drewsum/Nixie_Clock/rev_a/Nixie Clock/Nixie Clock Poster/RefDes.pdf

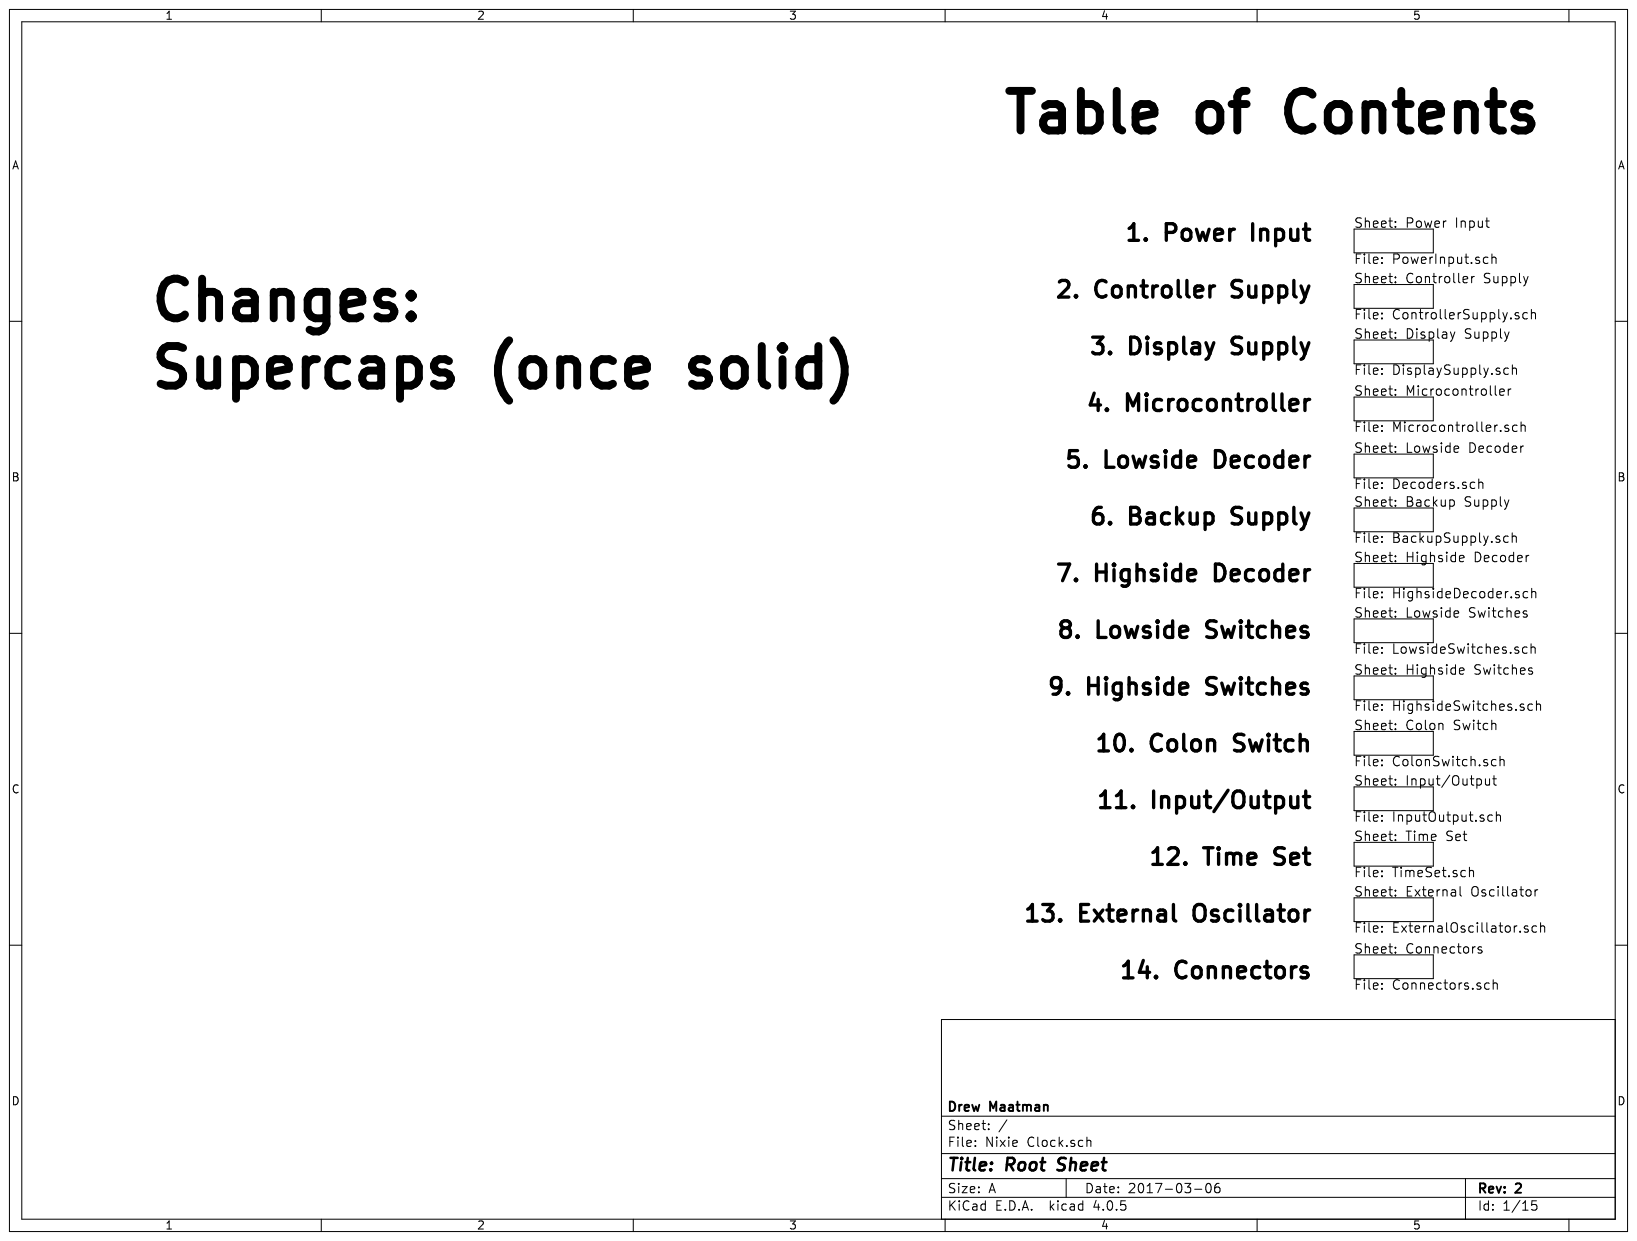
[picture p72: page 1]






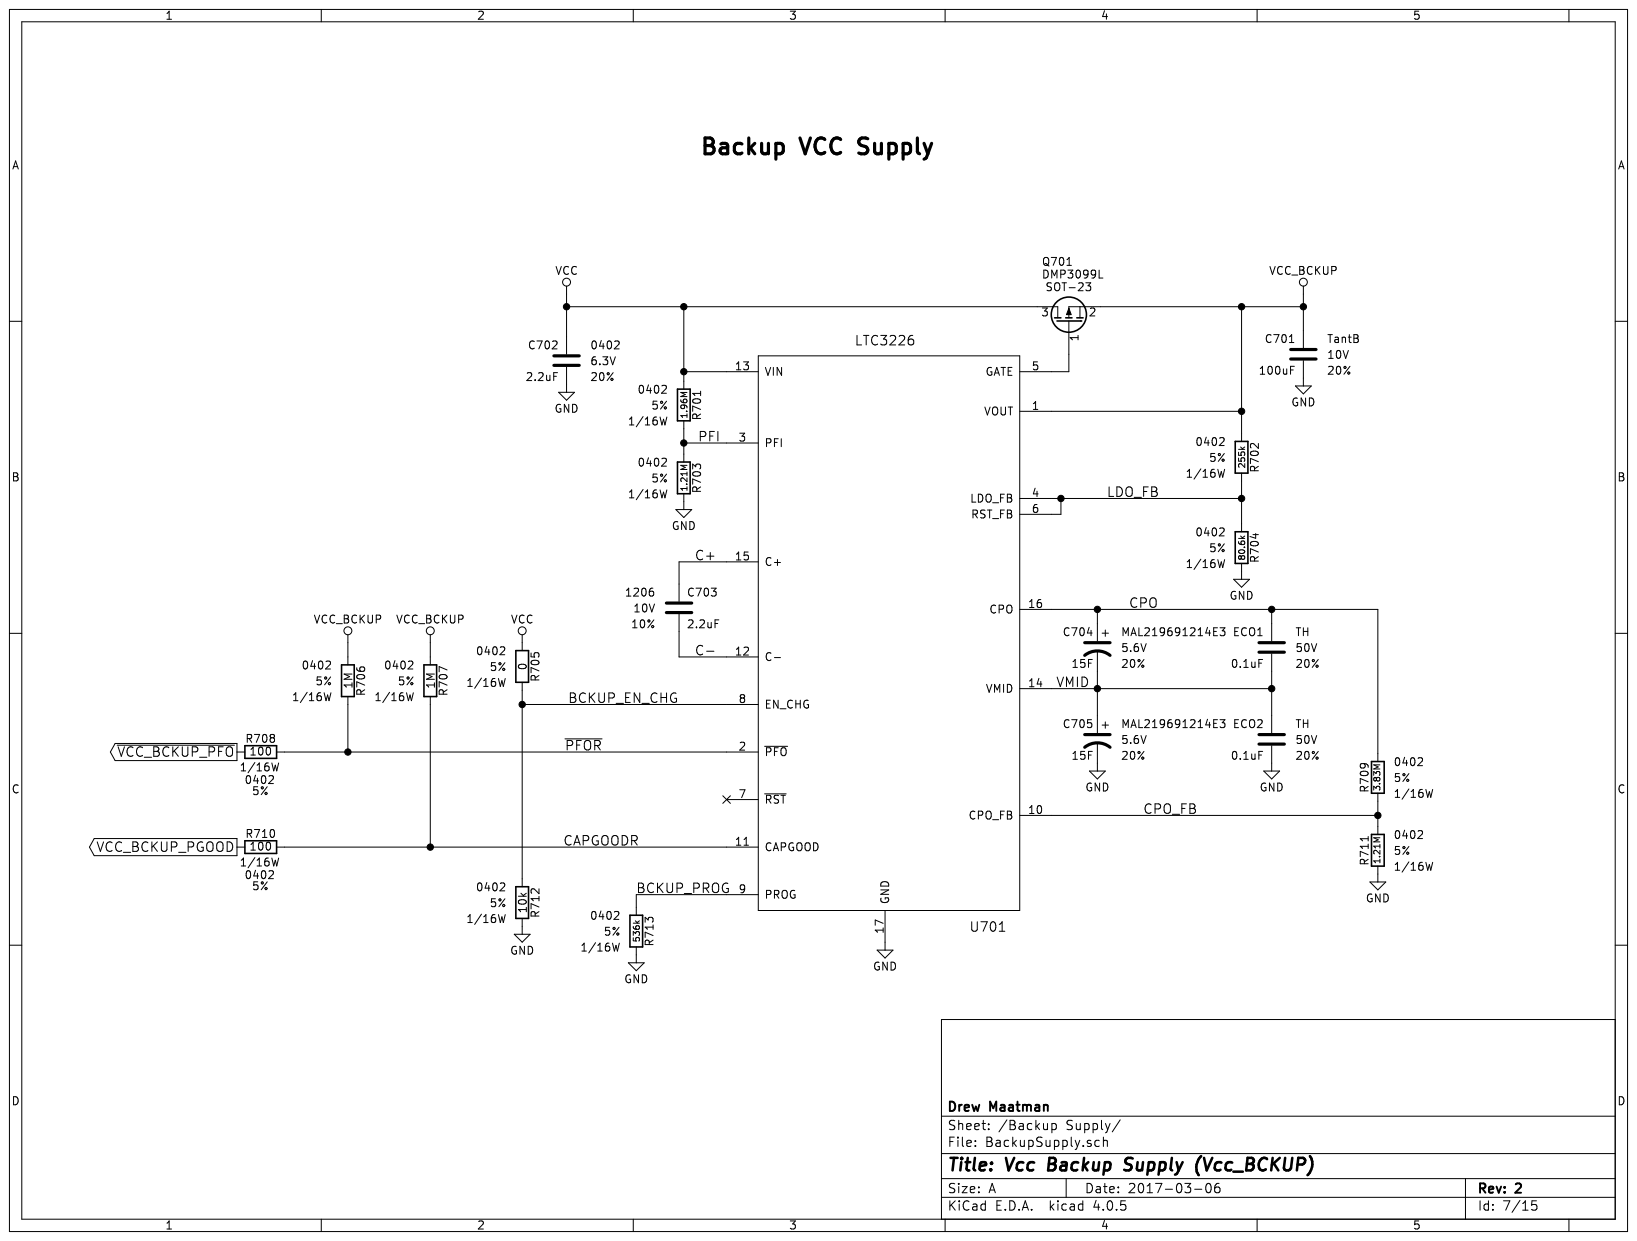
[picture p73: page 7]
