drewsum/Nixie_Clock/rev_b/hdw/Nixie_Clock_Core/design_files/POS180_boost.asc

C1: cap; 0.1µ
C2: cap; .01µ
C3: polcap; 4.7µ
C4: cap; 0.01µ
C5: cap; 0.1µ
C6: cap; 0.1µ
C7: cap; 1.5µ
D1: diode; RRU1LAM4S
D2: diode; RRU1LAM4S
D3: diode; RRU1LAM4S
I1: current; PULSE(0 5m 20m 0.1u 0.1u 0.5m 1m)
L1: ind; 680µ
Q1: NMOS; IRFP240
R1: RES; 14k
R2: res; 28.7k
R3: res; 1.6Meg
R4: res; 100k
R5: res; 330
R6: res; 200K
R7: res; 0.36
R8: res; 3.4k
R9: res; 1.6Meg
R10: res; 10k
R11: res; 1.33k
R12: res; 6.49k
R13: res; 1.6Meg
R14: res; 10k
U1: LT3757A
U2: LT6700-1
U3: LT6700-1
V1: VOLTAGE; 24
V2: voltage; 3.3
Named nets: 0, IN, POS180, POS90, pos3p3, pos180_pgood, pos90_pgood
.tran 100m startup
