drewsum/Nixie_Clock/rev_b/sfw/U1001_Firmware/Nixie_Clock.X/temperature_sensors.h

/* ************************************************************************** */
/** Descriptive File Name

  @Company
    Company Name

  @File Name
    filename.h

  @Summary
    Brief description of the file.

  @Description
    Describe the purpose of this file.
 */
/* ************************************************************************** */

#ifndef _TEMPERATURE_SENSORS_H    /* Guard against multiple inclusion */
#define _TEMPERATURE_SENSORS_H

#include "mcp9804_temp_sensor.h"

#include "error_handler.h"

// These are all the I2C 7 bit addresses of temperature sensors in this project
#define POS24_TEMP_SNS_ADDR         0x18
#define POS3P3_TEMP_SNS_ADDR        0x19
#define POS180_TEMP_SNS_ADDR        0x1A
#define AMB_TEMP_SNS_ADDR           0x1C

volatile __attribute__((coherent)) uint8_t temp_sense_data_request = 0;

// This function initializes all temperature sensors in the project, if available
void tempSensorsInitialize(void);

// this function gets temperature data for all temperature sensors
void tempSensorsRetrieveData(void);

// this function prints out the status for all temperature sensors
void printTemperatureSensorStatus(void);

#endif /* _TEMPERATURE_SENSORS_H */

/* *****************************************************************************
 End of File
 */
