drewsum/Nixie_Clock/rev_b/sfw/U1001_Firmware/Nixie_Clock.X/adc_channels.c

#include "adc_channels.h"

#include <stdio.h>

#include "32mz_interrupt_control.h"
#include "telemetry.h"
#include "terminal_control.h"
#include "pin_macros.h"

/*
 * 
 * Used ADC channels: 
 * 
 * AN19 - POS90_ADC
 * AN20 - POS180_ADC
 * AN21 - VBAT ADC
 * AN43 - Internal VREF
 * AN44 - Die Temp
 * 
 * */

// this function sets up ADC channels
void adcChannelsInitialize(void) {
 
    /* Select ADC input mode for each channel*/
    ADCIMCON2bits.DIFF19 = 0; // Single ended mode
    ADCIMCON2bits.SIGN19 = 0; // unsigned data format
    ADCIMCON2bits.DIFF20 = 0; // Single ended mode
    ADCIMCON2bits.SIGN20 = 0; // unsigned data format
    if (RTC_HARDSTRAP_PIN == 0) {
        ADCIMCON2bits.DIFF21 = 0; // Single ended mode
        ADCIMCON2bits.SIGN21 = 0; // unsigned data format
    }
    ADCIMCON3bits.DIFF43 = 0; // Single ended mode
    ADCIMCON3bits.SIGN43 = 0; // unsigned data format
    ADCIMCON3bits.DIFF44 = 0; // Single ended mode
    ADCIMCON3bits.SIGN44 = 0; // unsigned data format
    
    /* Configure interrupt enables */
    ADCGIRQEN1bits.AGIEN19 = 1;     // enable data ready 19 IRQ
    ADCGIRQEN1bits.AGIEN20 = 1;     // enable data ready 20 IRQ
    if (RTC_HARDSTRAP_PIN == 0) ADCGIRQEN1bits.AGIEN21 = 1;     // enable data ready 21 IRQ
    ADCGIRQEN2bits.AGIEN43 = 1;     // enable data ready 43 IRQ
    ADCGIRQEN2bits.AGIEN44 = 1;     // enable data ready 44 IRQ
    
    // set IRQ priorities
    setInterruptPriority(ADC_Data_19, 1);
    setInterruptPriority(ADC_Data_20, 1);
    if (RTC_HARDSTRAP_PIN == 0) setInterruptPriority(ADC_Data_21, 1);
    setInterruptPriority(ADC_Data_43, 1);
    setInterruptPriority(ADC_Data_44, 1);
    
    // set IRQ subpriorities
    setInterruptSubpriority(ADC_Data_19, 1);
    setInterruptSubpriority(ADC_Data_20, 1);
    if (RTC_HARDSTRAP_PIN == 0) setInterruptSubpriority(ADC_Data_21, 1);
    setInterruptSubpriority(ADC_Data_43, 2);
    setInterruptSubpriority(ADC_Data_44, 3);
    
    /* Configure common scan */
    ADCCSS1bits.CSS19 = 1;          // Enable Channel 19 for common scan
    ADCCSS1bits.CSS20 = 1;          // Enable Channel 20 for common scan
    if (RTC_HARDSTRAP_PIN == 0) ADCCSS1bits.CSS21 = 1;          // Enable Channel 21 for common scan
    ADCCSS2bits.CSS43 = 1;          // Enable Channel 43 for common scan
    ADCCSS2bits.CSS44 = 1;          // Enable Channel 44 for common scan
    
    // clear interrupt flags
    clearInterruptFlag(ADC_Data_19);
    clearInterruptFlag(ADC_Data_20);
    if (RTC_HARDSTRAP_PIN == 0) clearInterruptFlag(ADC_Data_21);
    clearInterruptFlag(ADC_Data_43);
    clearInterruptFlag(ADC_Data_44);
    
    // enable data ready interrupts
    enableInterrupt(ADC_Data_19);
    enableInterrupt(ADC_Data_20);
    if (RTC_HARDSTRAP_PIN == 0) enableInterrupt(ADC_Data_21);
    enableInterrupt(ADC_Data_43);
    enableInterrupt(ADC_Data_44);
    
}

void __ISR(_ADC_DATA19_VECTOR, IPL1SRS) ADCData19ISR(void) {

    // check to see if data is actually ready
    if (ADCDSTAT1bits.ARDY19) {
        // copy ADC conversion result into telemetry
        telemetry.pos90_termination_voltage = ((double) ADCDATA19) * ADC_VOLTS_PER_LSB * adc_cal_gain * POS90_ADC_GAIN;
        
    }
    
    // clear IRQ
    clearInterruptFlag(ADC_Data_19);
    
}

void __ISR(_ADC_DATA20_VECTOR, IPL1SRS) ADCData20ISR(void) {

    // check to see if data is actually ready
    if (ADCDSTAT1bits.ARDY20) {
        // copy ADC conversion result into telemetry
        telemetry.pos180.voltage =((double) ADCDATA20) * ADC_VOLTS_PER_LSB * adc_cal_gain * POS180_ADC_GAIN;
        
    }
    
    // clear IRQ
    clearInterruptFlag(ADC_Data_20);
    
}

void __ISR(_ADC_DATA21_VECTOR, IPL1SRS) ADCData21ISR(void) {

    // check to see if data is actually ready
    if (ADCDSTAT1bits.ARDY21) {
        // copy ADC conversion result into telemetry
        telemetry.backup_battery_voltage = ((double) ADCDATA21) * ADC_VOLTS_PER_LSB * adc_cal_gain * VBAT_ADC_GAIN;
        
    }
    
    // clear IRQ
    clearInterruptFlag(ADC_Data_21);
    
}

void __ISR(_ADC_DATA43_VECTOR, IPL1SRS) ADCData43ISR(void) {

    // check to see if data is actually ready
    if (ADCDSTAT2bits.ARDY43) {
        // copy ADC conversion result into telemetry
        telemetry.adc_vref_voltage = (double) ADCDATA43 * ADC_VOLTS_PER_LSB;
        // compensate for errors in the ADC, we know VREF is supposed to be 1.2V
        adc_cal_gain = (1.2 / telemetry.adc_vref_voltage);
        
    }
    
    // clear IRQ
    clearInterruptFlag(ADC_Data_43);
    
}

void __ISR(_ADC_DATA44_VECTOR, IPL1SRS) ADCData44ISR(void) {
    
    // check to see if data is actually ready
    if (ADCDSTAT2bits.ARDY44) {

        // copy ADC conversion result into telemetry
        telemetry.mcu_die_temp = (double) ((ADCDATA44 * ADC_VOLTS_PER_LSB * adc_cal_gain) - 0.7) / 0.005 + HOST_TEMP_OFFSET;
        
    }
    
    // clear IRQ
    clearInterruptFlag(ADC_Data_44);
    
}

// this function prints out ADC channel status
void printADCChannelStatus(void) {
 
    // print out presence of each analog input
    if (ADCSYSCFG0bits.AN0) terminalTextAttributes(GREEN_COLOR, BLACK_COLOR, NORMAL_FONT);
    else terminalTextAttributes(RED_COLOR, BLACK_COLOR, NORMAL_FONT);
    printf("    Channel AN0 is %s\n\r", ADCSYSCFG0bits.AN0 ? "present" : "absent");
    if (ADCSYSCFG0bits.AN1) terminalTextAttributes(GREEN_COLOR, BLACK_COLOR, NORMAL_FONT);
    else terminalTextAttributes(RED_COLOR, BLACK_COLOR, NORMAL_FONT);
    printf("    Channel AN1 is %s\n\r", ADCSYSCFG0bits.AN1 ? "present" : "absent");
    if (ADCSYSCFG0bits.AN2) terminalTextAttributes(GREEN_COLOR, BLACK_COLOR, NORMAL_FONT);
    else terminalTextAttributes(RED_COLOR, BLACK_COLOR, NORMAL_FONT);
    printf("    Channel AN2 is %s\n\r", ADCSYSCFG0bits.AN2 ? "present" : "absent");
    if (ADCSYSCFG0bits.AN3) terminalTextAttributes(GREEN_COLOR, BLACK_COLOR, NORMAL_FONT);
    else terminalTextAttributes(RED_COLOR, BLACK_COLOR, NORMAL_FONT);
    printf("    Channel AN3 is %s\n\r", ADCSYSCFG0bits.AN3 ? "present" : "absent");
    if (ADCSYSCFG0bits.AN3) terminalTextAttributes(GREEN_COLOR, BLACK_COLOR, NORMAL_FONT);
    else terminalTextAttributes(RED_COLOR, BLACK_COLOR, NORMAL_FONT);
    printf("    Channel AN3 is %s\n\r", ADCSYSCFG0bits.AN3 ? "present" : "absent");
    if (ADCSYSCFG0bits.AN4) terminalTextAttributes(GREEN_COLOR, BLACK_COLOR, NORMAL_FONT);
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
//    else terminalTextAttributes(RED_COLOR, BLACK_COLOR, NORMAL_FONT);
//    printf("    Channel AN63 data interrupt %s\n\r\n\r", ADCGIRQEN2bits.AGIEN63 ? "enabled" : "disabled");
    
    terminalTextAttributesReset();
    
}
