drewsum/Nixie_Clock/rev_b/sfw/U1001_Firmware/Nixie_Clock.X/plib_i2c.c

/*******************************************************************************
  Inter-Integrated Circuit (I2C) Library
  Source File

  Company:
    Microchip Technology Inc.

  File Name:
    plib_i2c.c

  Summary:
    I2C PLIB Implementation file

  Description:
    This file defines the interface to the I2C peripheral library.
    This library provides access to and control of the associated peripheral
    instance.

*******************************************************************************/
// DOM-IGNORE-BEGIN
/*******************************************************************************
* Copyright (C) 2018-2019 Microchip Technology Inc. and its subsidiaries.
*
* Subject to your compliance with these terms, you may use Microchip software
* and any derivatives exclusively with Microchip products. It is your
* responsibility to comply with third party license terms applicable to your
* use of third party software (including open source software) that may
* accompany Microchip software.
*
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
* IN NO EVENT WILL MICROCHIP BE LIABLE FOR ANY INDIRECT, SPECIAL, PUNITIVE,
* INCIDENTAL OR CONSEQUENTIAL LOSS, DAMAGE, COST OR EXPENSE OF ANY KIND
* WHATSOEVER RELATED TO THE SOFTWARE, HOWEVER CAUSED, EVEN IF MICROCHIP HAS
* BEEN ADVISED OF THE POSSIBILITY OR THE DAMAGES ARE FORESEEABLE. TO THE
* FULLEST EXTENT ALLOWED BY LAW, MICROCHIP'S TOTAL LIABILITY ON ALL CLAIMS IN
* ANY WAY RELATED TO THIS SOFTWARE WILL NOT EXCEED THE AMOUNT OF FEES, IF ANY,
* THAT YOU HAVE PAID DIRECTLY TO MICROCHIP FOR THIS SOFTWARE.
*******************************************************************************/
// DOM-IGNORE-END

// *****************************************************************************
// *****************************************************************************
// Section: Included Files
// *****************************************************************************
// *****************************************************************************

#include "plib_i2c.h"
#include "32mz_interrupt_control.h"
#include <xc.h>

#include <stdio.h>

#include "terminal_control.h"
#include "error_handler.h"

// These are macros needed for defining ISRs, included in XC52
#include <sys/attribs.h>

// *****************************************************************************
// *****************************************************************************
// Section: Global Data
// *****************************************************************************
// *****************************************************************************


void I2CMaster_Initialize(void)
{
    /* Disable the I2C Master interrupt */
    disableInterrupt(I2C_MASTER_INT_SOURCE);
    
    /* Disable the I2C Bus collision interrupt */
    disableInterrupt(I2C_BUS_COL_INT_SOURCE);

    I2C_MASTER_BRG_REG = 0x055;

    I2C_MASTER_CON_BITFIELD.SIDL = 0;
    I2C_MASTER_CON_BITFIELD.DISSLW = 0;
    I2C_MASTER_CON_BITFIELD.SMEN = 0;

    setInterruptPriority(I2C_BUS_COL_INT_SOURCE, 4);
    setInterruptPriority(I2C_MASTER_INT_SOURCE, 7);
    
    /* Clear master interrupt flag */
    clearInterruptFlag(I2C_MASTER_INT_SOURCE);

    /* Clear fault interrupt flag */
    clearInterruptFlag(I2C_BUS_COL_INT_SOURCE);

    /* Turn on the I2C module */
    I2C_MASTER_CON_BITFIELD.ON = 1;

    /* Set the initial state of the I2C state machine */
    i2cMasterObj.state = I2C_STATE_IDLE;
}

/* I2C state machine */
static void I2CMaster_TransferSM(void)
{
    clearInterruptFlag(I2C_MASTER_INT_SOURCE);

    switch (i2cMasterObj.state)
    {
        case I2C_STATE_START_CONDITION:
            /* Generate Start Condition */
            I2C_MASTER_CON_BITFIELD.SEN = 1;
            enableInterrupt(I2C_MASTER_INT_SOURCE);
            enableInterrupt(I2C_BUS_COL_INT_SOURCE);
            i2cMasterObj.state = I2C_STATE_ADDR_BYTE_1_SEND;
            break;

        case I2C_STATE_ADDR_BYTE_1_SEND:
            /* Is transmit buffer full? */
            if (!(I2C_MASTER_STAT_BITFIELD.TBF))
            {
                if (i2cMasterObj.address > 0x007F)
                {
                    /* Transmit the MSB 2 bits of the 10-bit slave address, with R/W = 0 */
                    I2C_MASTER_TRN_REG = ( 0xF0 | (((uint8_t*)&i2cMasterObj.address)[1] << 1));

                    i2cMasterObj.state = I2C_STATE_ADDR_BYTE_2_SEND;
                }
                else
                {
                    /* 8-bit addressing mode */
                    I2C_MASTER_TRN_REG = ((i2cMasterObj.address << 1) | i2cMasterObj.transferType);

                    if (i2cMasterObj.transferType == I2C_TRANSFER_TYPE_WRITE)
                    {
                        i2cMasterObj.state = I2C_STATE_WRITE;
                    }
                    else
                    {
                        i2cMasterObj.state = I2C_STATE_READ;
                    }
                }
            }
            break;

        case I2C_STATE_ADDR_BYTE_2_SEND:
            /* Transmit the 2nd byte of the 10-bit slave address */
            if (!(I2C_MASTER_STAT_BITFIELD.ACKSTAT))
            {
                if (!(I2C_MASTER_STAT_BITFIELD.TBF))
                {
                    /* Transmit the remaining 8-bits of the 10-bit address */
                    I2C_MASTER_TRN_REG = i2cMasterObj.address;

                    if (i2cMasterObj.transferType == I2C_TRANSFER_TYPE_WRITE)
                    {
                        i2cMasterObj.state = I2C_STATE_WRITE;
                    }
                    else
                    {
                        i2cMasterObj.state = I2C_STATE_READ_10BIT_MODE;
                    }
                }
            }
            else
            {
                /* NAK received. Generate Stop Condition. */
                i2cMasterObj.error = I2C_ERROR_NACK;
                I2C_MASTER_CON_BITFIELD.PEN = 1;
                i2cMasterObj.state = I2C_STATE_WAIT_STOP_CONDITION_COMPLETE;
            }
            break;

        case I2C_STATE_READ_10BIT_MODE:
            if (!(I2C_MASTER_STAT_BITFIELD.ACKSTAT))
            {
                /* Generate repeated start condition */
                I2C_MASTER_CON_BITFIELD.RSEN = 1;
                i2cMasterObj.state = I2C_STATE_ADDR_BYTE_1_SEND_10BIT_ONLY;
            }
            else
            {
                /* NAK received. Generate Stop Condition. */
                i2cMasterObj.error = I2C_ERROR_NACK;
                I2C_MASTER_CON_BITFIELD.PEN = 1;
                i2cMasterObj.state = I2C_STATE_WAIT_STOP_CONDITION_COMPLETE;
            }
            break;

        case I2C_STATE_ADDR_BYTE_1_SEND_10BIT_ONLY:
            /* Is transmit buffer full? */
            if (!(I2C_MASTER_STAT_BITFIELD.TBF))
            {
                /* Transmit the first byte of the 10-bit slave address, with R/W = 1 */
                I2C_MASTER_TRN_REG = ( 0xF1 | ((((uint8_t*)&i2cMasterObj.address)[1] << 1)));
                i2cMasterObj.state = I2C_STATE_READ;
            }
            else
            {
                /* NAK received. Generate Stop Condition. */
                i2cMasterObj.error = I2C_ERROR_NACK;
                I2C_MASTER_CON_BITFIELD.PEN = 1;
                i2cMasterObj.state = I2C_STATE_WAIT_STOP_CONDITION_COMPLETE;
            }
            break;

        case I2C_STATE_WRITE:
            if (!(I2C_MASTER_STAT_BITFIELD.ACKSTAT))
            {
                /* ACK received */
                if (i2cMasterObj.writeCount < i2cMasterObj.writeSize)
                {
                    if (!(I2C_MASTER_STAT_BITFIELD.TBF))
                    {
                        /* Transmit the data from writeBuffer[] */
                        I2C_MASTER_TRN_REG = i2cMasterObj.writeBuffer[i2cMasterObj.writeCount++];
                    }
                }
                else
                {
                    if (i2cMasterObj.readCount < i2cMasterObj.readSize)
                    {
                        /* Generate repeated start condition */
                        I2C_MASTER_CON_BITFIELD.RSEN = 1;

                        i2cMasterObj.transferType = I2C_TRANSFER_TYPE_READ;

                        if (i2cMasterObj.address > 0x007F)
                        {
                            /* Send the I2C slave address with R/W = 1 */
                            i2cMasterObj.state = I2C_STATE_ADDR_BYTE_1_SEND_10BIT_ONLY;
                        }
                        else
                        {
                            /* Send the I2C slave address with R/W = 1 */
                            i2cMasterObj.state = I2C_STATE_ADDR_BYTE_1_SEND;
                        }

                    }
                    else
                    {
                        /* Transfer Complete. Generate Stop Condition */
                        I2C_MASTER_CON_BITFIELD.PEN = 1;
                        i2cMasterObj.state = I2C_STATE_WAIT_STOP_CONDITION_COMPLETE;
                    }
                }
            }
            else
            {
                /* NAK received. Generate Stop Condition. */
                i2cMasterObj.error = I2C_ERROR_NACK;
                I2C_MASTER_CON_BITFIELD.PEN = 1;
                i2cMasterObj.state = I2C_STATE_WAIT_STOP_CONDITION_COMPLETE;
            }
            break;

        case I2C_STATE_READ:
            if (!(I2C_MASTER_STAT_BITFIELD.ACKSTAT))
            {
                /* Slave ACK'd the device address. Enable receiver. */
                I2C_MASTER_CON_BITFIELD.RCEN = 1;
                i2cMasterObj.state = I2C_STATE_READ_BYTE;
            }
            else
            {
                /* NAK received. Generate Stop Condition. */
                i2cMasterObj.error = I2C_ERROR_NACK;
                I2C_MASTER_CON_BITFIELD.PEN = 1;
                i2cMasterObj.state = I2C_STATE_WAIT_STOP_CONDITION_COMPLETE;
            }
            break;

        case I2C_STATE_READ_BYTE:
            /* Data received from the slave */
            if (I2C_MASTER_STAT_BITFIELD.RBF)
            {
                i2cMasterObj.readBuffer[i2cMasterObj.readCount++] = I2C_MASTER_RCV_REG;
                if (i2cMasterObj.readCount == i2cMasterObj.readSize)
                {
                    /* Send NAK */
                    I2C_MASTER_CON_BITFIELD.ACKDT = 1;
                    I2C_MASTER_CON_BITFIELD.ACKEN = 1;
                }
                else
                {
                    /* Send ACK */
                    I2C_MASTER_CON_BITFIELD.ACKDT = 0;
                    I2C_MASTER_CON_BITFIELD.ACKEN = 1;
                }
                i2cMasterObj.state = I2C_STATE_WAIT_ACK_COMPLETE;
            }
            break;

        case I2C_STATE_WAIT_ACK_COMPLETE:
            /* ACK or NAK sent to the I2C slave */
            if (i2cMasterObj.readCount < i2cMasterObj.readSize)
            {
                /* Enable receiver */
                I2C_MASTER_CON_BITFIELD.RCEN = 1;
                i2cMasterObj.state = I2C_STATE_READ_BYTE;
            }
            else
            {
                /* Generate Stop Condition */
                I2C_MASTER_CON_BITFIELD.PEN = 1;
                i2cMasterObj.state = I2C_STATE_WAIT_STOP_CONDITION_COMPLETE;
            }
            break;

        case I2C_STATE_WAIT_STOP_CONDITION_COMPLETE:
            i2cMasterObj.state = I2C_STATE_IDLE;
            disableInterrupt(I2C_MASTER_INT_SOURCE);
            disableInterrupt(I2C_BUS_COL_INT_SOURCE);
            if (i2cMasterObj.callback != NULL)
            {
                i2cMasterObj.callback(i2cMasterObj.context);
            }
            break;

        default:
            break;
    }
}


void I2CMaster_CallbackRegister(I2C_CALLBACK callback, uintptr_t contextHandle)
{
    if (callback == NULL)
    {
        return;
    }

    i2cMasterObj.callback = callback;
    i2cMasterObj.context = contextHandle;
}

bool I2CMaster_IsBusy(void)
{
    if( (i2cMasterObj.state != I2C_STATE_IDLE ) || (I2C_MASTER_CON_REG & 0x0000001F) ||
        (I2C_MASTER_STAT_BITFIELD.TRSTAT) || (I2C_MASTER_STAT_BITFIELD.S) )
    {
        return true;
    }
    else
    {
        return false;
    }
}

bool I2CMaster_Read(uint16_t address, uint8_t* rdata, size_t rlength)
{
    /* State machine must be idle and I2C module should not have detected a start bit on the bus */
    if((i2cMasterObj.state != I2C_STATE_IDLE) || (I2C_MASTER_STAT_BITFIELD.S))
    {
        return false;
    }

    i2cMasterObj.address             = address;
    i2cMasterObj.readBuffer          = rdata;
    i2cMasterObj.readSize            = rlength;
    i2cMasterObj.writeBuffer         = NULL;
    i2cMasterObj.writeSize           = 0;
    i2cMasterObj.writeCount          = 0;
    i2cMasterObj.readCount           = 0;
    i2cMasterObj.transferType        = I2C_TRANSFER_TYPE_READ;
    i2cMasterObj.error               = I2C_ERROR_NONE;
    i2cMasterObj.state               = I2C_STATE_ADDR_BYTE_1_SEND;

    I2C_MASTER_CON_BITFIELD.SEN = 1;
    enableInterrupt(I2C_MASTER_INT_SOURCE);
    enableInterrupt(I2C_BUS_COL_INT_SOURCE);

    return true;
}


bool I2CMaster_Write(uint16_t address, uint8_t* wdata, size_t wlength)
{
    /* State machine must be idle and I2C module should not have detected a start bit on the bus */
    if((i2cMasterObj.state != I2C_STATE_IDLE) || (I2C_MASTER_STAT_BITFIELD.S))
    {
        return false;
    }

    i2cMasterObj.address             = address;
    i2cMasterObj.readBuffer          = NULL;
    i2cMasterObj.readSize            = 0;
    i2cMasterObj.writeBuffer         = wdata;
    i2cMasterObj.writeSize           = wlength;
    i2cMasterObj.writeCount          = 0;
    i2cMasterObj.readCount           = 0;
    i2cMasterObj.transferType        = I2C_TRANSFER_TYPE_WRITE;
    i2cMasterObj.error               = I2C_ERROR_NONE;
    i2cMasterObj.state               = I2C_STATE_ADDR_BYTE_1_SEND;

    I2C_MASTER_CON_BITFIELD.SEN = 1;
    enableInterrupt(I2C_MASTER_INT_SOURCE);
    enableInterrupt(I2C_BUS_COL_INT_SOURCE);

    return true;
}


bool I2CMaster_WriteRead(uint16_t address, uint8_t* wdata, size_t wlength, uint8_t* rdata, size_t rlength)
{
    /* State machine must be idle and I2C module should not have detected a start bit on the bus */
    if((i2cMasterObj.state != I2C_STATE_IDLE) || (I2C_MASTER_STAT_BITFIELD.S))
    {
        return false;
    }

    i2cMasterObj.address             = address;
    i2cMasterObj.readBuffer          = rdata;
    i2cMasterObj.readSize            = rlength;
    i2cMasterObj.writeBuffer         = wdata;
    i2cMasterObj.writeSize           = wlength;
    i2cMasterObj.writeCount          = 0;
    i2cMasterObj.readCount           = 0;
    i2cMasterObj.transferType        = I2C_TRANSFER_TYPE_WRITE;
    i2cMasterObj.error               = I2C_ERROR_NONE;
    i2cMasterObj.state               = I2C_STATE_ADDR_BYTE_1_SEND;

    I2C_MASTER_CON_BITFIELD.SEN = 1;
    enableInterrupt(I2C_MASTER_INT_SOURCE);
    enableInterrupt(I2C_BUS_COL_INT_SOURCE);

    return true;
}

I2C_ERROR I2CMaster_ErrorGet(void)
{
    I2C_ERROR error;

    error = i2cMasterObj.error;
    i2cMasterObj.error = I2C_ERROR_NONE;

    return error;
}

bool I2CMaster_TransferSetup(I2C_TRANSFER_SETUP* setup, uint32_t srcClkFreq )
{
    uint32_t baudValue;
    uint32_t i2cClkSpeed;

    if (setup == NULL)
    {
        return false;
    }

    i2cClkSpeed = setup->clkSpeed;

    /* Maximum I2C clock speed cannot be greater than 1 MHz */
    if (i2cClkSpeed > 1000000)
    {
        return false;
    }

    if( srcClkFreq == 0)
    {
        srcClkFreq = 6666666UL;
    }

    baudValue = ((float)((float)srcClkFreq/2.0) * (1/(float)i2cClkSpeed - 0.000000150)) - 1;

    /* I2CxBRG value cannot be from 0 to 5 or more than the size of the baud rate register */
    if ((baudValue < 4) || (baudValue > 65555))
    {
        return false;
    }

    I2C_MASTER_BRG_REG = baudValue;

    /* Enable slew rate for 400 kHz clock speed; disable for all other speeds */

    if (i2cClkSpeed == 400000)
    {
        I2C_MASTER_CON_BITFIELD.DISSLW = 0;;
    }
    else
    {
        I2C_MASTER_CON_BITFIELD.DISSLW = 1;
    }

    return true;
}

void __ISR(I2C_MASTER_BUS_COL_VECTOR, IPL4SRS) I2CMaster_BUS_InterruptHandler( void )
{
    
    /* Clear the bus collision error status bit */
    I2C_MASTER_STAT_BITFIELD.BCL = 0;

    /* ACK the bus interrupt */
    clearInterruptFlag(I2C_BUS_COL_INT_SOURCE);

    i2cMasterObj.state = I2C_STATE_IDLE;

    i2cMasterObj.error = I2C_ERROR_BUS_COLLISION;

    if (i2cMasterObj.callback != NULL)
    {
        i2cMasterObj.callback(i2cMasterObj.context);
    }
    
    // enter bus collision handling code here
	clearInterruptFlag(I2C_BUS_COL_INT_SOURCE);
    // error_handler.flags.i2c_bus_collision = 1;
} 

void __ISR(I2C_MASTER_INT_VECTOR, IPL7SRS) I2C_MASTER_ISR ( void )
{
    I2CMaster_TransferSM();
}

// this function prints out status about the I2C module used in master mode
void printI2CMasterStatus(void) {
    
    // print I2CXCON bitfield
    if (I2C_MASTER_CON_BITFIELD.ON) terminalTextAttributes(GREEN_COLOR, BLACK_COLOR, NORMAL_FONT);
    else terminalTextAttributes(RED_COLOR, BLACK_COLOR, NORMAL_FONT);
    printf("    I2C Master Module is %s\n\r", I2C_MASTER_CON_BITFIELD.ON ? "enabled" : "disabled");
    
    terminalTextAttributes(GREEN_COLOR, BLACK_COLOR, NORMAL_FONT);
    printf("    I2C SDA hold time set to %s\n\r", I2C_MASTER_CON_BITFIELD.SDAHT ? "500ns" : "100ns");
    
    if (I2C_MASTER_CON_BITFIELD.SIDL) terminalTextAttributes(RED_COLOR, BLACK_COLOR, NORMAL_FONT);
    else terminalTextAttributes(GREEN_COLOR, BLACK_COLOR, NORMAL_FONT);
    printf("    I2C Master Module %s in Idle Mode\n\r", I2C_MASTER_CON_BITFIELD.SIDL ? "Disabled" : "Enabled");
    
    if (I2C_MASTER_CON_BITFIELD.STRICT) terminalTextAttributes(GREEN_COLOR, BLACK_COLOR, NORMAL_FONT);
    else terminalTextAttributes(RED_COLOR, BLACK_COLOR, NORMAL_FONT);
    printf("    Strict address enforcement is %s\n\r", I2C_MASTER_CON_BITFIELD.STRICT ? "enabled" : "disabled");
    
    if (I2C_MASTER_CON_BITFIELD.A10M) terminalTextAttributes(GREEN_COLOR, BLACK_COLOR, NORMAL_FONT);
    else terminalTextAttributes(RED_COLOR, BLACK_COLOR, NORMAL_FONT);
    printf("    10 bit addressing is %s\n\r", I2C_MASTER_CON_BITFIELD.A10M ? "enabled" : "disabled");
    
    if (I2C_MASTER_CON_BITFIELD.DISSLW) terminalTextAttributes(RED_COLOR, BLACK_COLOR, NORMAL_FONT);
    else terminalTextAttributes(GREEN_COLOR, BLACK_COLOR, NORMAL_FONT);
    printf("    Drive strength slew rate control is %s\n\r", I2C_MASTER_CON_BITFIELD.DISSLW ? "disabled" : "enabled");
    
    terminalTextAttributes(GREEN_COLOR, BLACK_COLOR, NORMAL_FONT);
    printf("    I/O logic thresholds set to %s levels\n\r", I2C_MASTER_CON_BITFIELD.SMEN ? "SMBus" : "I2C");
    printf("    Next acknowledge sequence is a data %s\n\r", I2C_MASTER_CON_BITFIELD.ACKDT ? "NACK" : "ACK");
    
    if (I2C_MASTER_CON_BITFIELD.ACKEN) terminalTextAttributes(GREEN_COLOR, BLACK_COLOR, NORMAL_FONT);
    else terminalTextAttributes(RED_COLOR, BLACK_COLOR, NORMAL_FONT);
    printf("    Acknowledge sequence is currently %s\n\r", I2C_MASTER_CON_BITFIELD.ACKEN ? "Enabled" : "Disabled");
    
    if (I2C_MASTER_CON_BITFIELD.RCEN) terminalTextAttributes(GREEN_COLOR, BLACK_COLOR, NORMAL_FONT);
    else terminalTextAttributes(RED_COLOR, BLACK_COLOR, NORMAL_FONT);
    printf("    Master is currently %s\n\r", I2C_MASTER_CON_BITFIELD.RCEN ? "reading" : "writing");
    
    if (I2C_MASTER_CON_BITFIELD.PEN) terminalTextAttributes(GREEN_COLOR, BLACK_COLOR, NORMAL_FONT);
    else terminalTextAttributes(RED_COLOR, BLACK_COLOR, NORMAL_FONT);
    printf("    Stop condition is currently %s\n\r", I2C_MASTER_CON_BITFIELD.PEN ? "enabled" : "disabled");
    
    if (I2C_MASTER_CON_BITFIELD.RSEN) terminalTextAttributes(GREEN_COLOR, BLACK_COLOR, NORMAL_FONT);
    else terminalTextAttributes(RED_COLOR, BLACK_COLOR, NORMAL_FONT);
    printf("    Repeated start condition is %s\n\r", I2C_MASTER_CON_BITFIELD.RSEN ? "in progress" : "not in progress");
    
    if (I2C_MASTER_CON_BITFIELD.SEN) terminalTextAttributes(GREEN_COLOR, BLACK_COLOR, NORMAL_FONT);
    else terminalTextAttributes(RED_COLOR, BLACK_COLOR, NORMAL_FONT);
    printf("    Start condition is currently %s\n\r", I2C_MASTER_CON_BITFIELD.SEN ? "in progress" : "not in progress");
    
    // Print out bitfield for I2CXSTAT register
    if (I2C_MASTER_STAT_BITFIELD.ACKSTAT) terminalTextAttributes(GREEN_COLOR, BLACK_COLOR, NORMAL_FONT);
    else terminalTextAttributes(RED_COLOR, BLACK_COLOR, NORMAL_FONT);
    printf("    %s received from slave\n\r", I2C_MASTER_STAT_BITFIELD.ACKSTAT ? "NACK" : "ACK");
    
    if (I2C_MASTER_STAT_BITFIELD.TRSTAT) terminalTextAttributes(GREEN_COLOR, BLACK_COLOR, NORMAL_FONT);
    else terminalTextAttributes(RED_COLOR, BLACK_COLOR, NORMAL_FONT);
    printf("    Master transmit is currently %s\n\r", I2C_MASTER_STAT_BITFIELD.TRSTAT ? "in progress" : "not in progress");
    
    if (I2C_MASTER_STAT_BITFIELD.BCL) terminalTextAttributes(RED_COLOR, BLACK_COLOR, NORMAL_FONT);
    else terminalTextAttributes(GREEN_COLOR, BLACK_COLOR, NORMAL_FONT);
    printf("    Bus collision %s\n\r", I2C_MASTER_STAT_BITFIELD.BCL ? "detected" : "not detected");
    
    if (I2C_MASTER_STAT_BITFIELD.ADD10) terminalTextAttributes(GREEN_COLOR, BLACK_COLOR, NORMAL_FONT);
    else terminalTextAttributes(RED_COLOR, BLACK_COLOR, NORMAL_FONT);
    printf("    10 bit address %s\n\r", I2C_MASTER_STAT_BITFIELD.ADD10 ? "matched" : "not matched");
    
    if (I2C_MASTER_STAT_BITFIELD.IWCOL) terminalTextAttributes(RED_COLOR, BLACK_COLOR, NORMAL_FONT);
    else terminalTextAttributes(GREEN_COLOR, BLACK_COLOR, NORMAL_FONT);
    printf("    Write collision has %s\n\r", I2C_MASTER_STAT_BITFIELD.IWCOL ? "occurred" : "not occurred");
    
    if (I2C_MASTER_STAT_BITFIELD.I2COV) terminalTextAttributes(RED_COLOR, BLACK_COLOR, NORMAL_FONT);
    else terminalTextAttributes(GREEN_COLOR, BLACK_COLOR, NORMAL_FONT);
    printf("    Receive overflow has %s\n\r", I2C_MASTER_STAT_BITFIELD.I2COV ? "occurred" : "not occurred");
    
    if (I2C_MASTER_STAT_BITFIELD.P) terminalTextAttributes(GREEN_COLOR, BLACK_COLOR, NORMAL_FONT);
    else terminalTextAttributes(RED_COLOR, BLACK_COLOR, NORMAL_FONT);
    printf("    Stop bit was %s\n\r", I2C_MASTER_STAT_BITFIELD.P ? "detected" : "not detected");
    
    if (I2C_MASTER_STAT_BITFIELD.S) terminalTextAttributes(GREEN_COLOR, BLACK_COLOR, NORMAL_FONT);
    else terminalTextAttributes(RED_COLOR, BLACK_COLOR, NORMAL_FONT);
    printf("    Start or repeated start %s\n\r", I2C_MASTER_STAT_BITFIELD.S ? "detected" : "not detected");
    
    terminalTextAttributes(GREEN_COLOR, BLACK_COLOR, NORMAL_FONT);
    printf("    Master is currently %s\n\r", I2C_MASTER_STAT_BITFIELD.R_W ? "reading" : "writing");
    
    if (I2C_MASTER_STAT_BITFIELD.RBF) terminalTextAttributes(GREEN_COLOR, BLACK_COLOR, NORMAL_FONT);
    else terminalTextAttributes(RED_COLOR, BLACK_COLOR, NORMAL_FONT);
    printf("    Receive buffer is currently %s\n\r", I2C_MASTER_STAT_BITFIELD.RBF ? "full" : "empty");
    
    if (I2C_MASTER_STAT_BITFIELD.TBF) terminalTextAttributes(GREEN_COLOR, BLACK_COLOR, NORMAL_FONT);
    else terminalTextAttributes(RED_COLOR, BLACK_COLOR, NORMAL_FONT);
    printf("    Transmit buffer is currently %s\n\r", I2C_MASTER_STAT_BITFIELD.TBF ? "full" : "empty");
    
    terminalTextAttributes(GREEN_COLOR, BLACK_COLOR, NORMAL_FONT);
    printf("    I2C Baud Rate Generator is set to 0x%04X\r\n", I2C_MASTER_BRG_REG);
    printf("    Current transmit buffer contents: 0x%02X\r\n", I2C_MASTER_TRN_REG);
    printf("    Current receive buffer contents: 0x%02X\r\n", I2C_MASTER_RCV_REG);
    
    terminalTextAttributesReset();
    
}
