drewsum/Nixie_Clock/rev_b/sfw/U1001_Firmware/Nixie_Clock.X/in12_carrier.h

/* ************************************************************************** */
/** Descriptive File Name

  @Company
    Company Name

  @File Name
    filename.h

  @Summary
    Brief description of the file.

  @Description
    Describe the purpose of this file.
 */
/* ************************************************************************** */

#ifndef _IN12_CARRIER_H    /* Guard against multiple inclusion */
#define _IN12_CARRIER_H


#include <xc.h>

#include "plib_i2c.h"
#include "lp5009_led_driver.h"
#include "tca9555_io_expander.h"
#include "ds1683_ETC.h"
#include "generic_multiplexing_timers.h"
#include "generic_carrier_input.h"

// These macros set the data to be sent to the display board GPIO expander
// to set display LEDs to show what in12_clock_display_state enum is set to
#define IN12_MENU_LEDS_DISPLAY_TIME_STATE           0b0000000000000001
#define IN12_MENU_LEDS_SET_TIME_STATE               0b0000000000000010
#define IN12_MENU_LEDS_DISPLAY_DATE_STATE           0b0000000000000100
#define IN12_MENU_LEDS_SET_DATE_STATE               0b0000000000001000
#define IN12_MENU_LEDS_DISPLAY_WEEKDAY_STATE        0b0000000000010000
#define IN12_MENU_LEDS_SET_WEEKDAY_STATE            0b0000000000100000
#define IN12_MENU_LEDS_DISPLAY_ALARM_STATE          0b0000000001000000
#define IN12_MENU_LEDS_SET_ALARM_STATE              0b0000000010000000
#define IN12_MENU_LEDS_ALARM_ENABLE_STATE           0b0000000100000000
#define IN12_MENU_LEDS_SET_24HR_MODE_STATE          0b0000001000000000
#define IN12_MENU_LEDS_SET_BRIGHTNESS_STATE         0b0000010000000000
#define IN12_MENU_LEDS_SET_COLOR_STATE              0b0000100000000000

// misc device I2C addresses
#define IN12_ETC_ADDR                           0x6F
#define IN12_BACKLIGHT_LED_DRIVER_1_ADDR        0x14
#define IN12_BACKLIGHT_LED_DRIVER_2_ADDR        0x15
#define IN12_BACKLIGHT_LED_DRIVER_3_ADDR        0x16
#define IN12_IO_EXPANDER_ADDR                   0x27

// these macros are used to set the color for the backlight LEDs
#define WHITE_BACKLIGHT_COLOR       255, 255, 255
#define BLACK_BACKLIGHT_COLOR       0, 0, 0
#define RED_BACKLIGHT_COLOR         255, 0, 0
#define GREEN_BACKLIGHT_COLOR       0, 255, 0
#define BLUE_BACKLIGHT_COLOR        0, 0, 255
#define YELLOW_BACKLIGHT_COLOR      255, 255, 0
#define MAGENTA_BACKLIGHT_COLOR     255, 0, 255
#define CYAN_BACKLIGHT_COLOR        0, 255, 255

// This enum keeps track of which IN12 tube we're currently driving
// This includes the six numerals as well as the two colons
enum active_tube_e {
    
    in12_tube_0 = 0,
    in12_tube_1 = 1,
    in12_right_colon = 2,
    in12_tube_2 = 3,
    in12_tube_3 = 4,
    in12_left_colon = 5,
    in12_tube_4 = 6,
    in12_tube_5 = 7
    
} in12_active_tube;

// this flag is used to keep track of if the display is showing 24hr time or
// 12 hr time. This is set high if we're showing 12hr time, and set low
// if we're showing 24hr time
volatile uint8_t in12_am_pm_enable = 1;

// This flag is what allows values to alternate on and off when setting them
// with capacitive pushbuttons
extern volatile uint8_t clock_set_blank_request;

// Set this flag to use the DP as an AM/PM indicator on tube 4
volatile __attribute__((coherent)) uint8_t in12_dp_anode_request = 0;

// This unsigned int is what's used to set brightness of the display
// brightness timer is set to 10 * this value
volatile __attribute__((coherent)) uint8_t in12_display_brightness_setting = 100;

// This struct holds alarm settings
// Lets you set alarm hours and minutes, as well as arm the alarm
volatile struct in12_clock_alarm_s {
    
    uint8_t in12_alarm_hour;
    uint8_t in12_alarm_minute;
    uint8_t in12_alarm_second;
    uint8_t in12_alarm_arm;
    
} in12_clock_alarm;

// This global enum keeps track of what we want to display on the VFD display
// This needs to be volatile because a bunch of different functions can modify it
enum in12_clock_display_state_e {
    
    in12_display_time_state = 0,
    in12_set_time_state = 1,
    in12_display_date_state = 2,
    in12_set_date_state = 3,
    in12_display_weekday_state = 4,
    in12_set_weekday_state = 5,
    in12_display_alarm_state = 6,
    in12_set_alarm_state = 7,
    in12_alarm_enable_state = 8,
    in12_set_24hr_mode_state = 9,
    in12_set_brightness_state = 10,
    in12_set_backlight_color_state = 11,
    in12_display_lamp_test = 12
    
} volatile in12_clock_display_state = 0;

// This enum keeps track of which time setting we're changing when the user wants
// to change the time (hours, minutes, seconds
enum in12_clock_time_setting_s {
    
    in12_set_time_hours_state = 0,
    in12_set_time_minutes_state = 1,
    in12_set_time_seconds_state = 2,
    in12_clock_time_setting_finished_state = 3
    
}
volatile in12_clock_time_setting = 3;

// This enum keeps track of which date setting we're changing when the user wants
// to change the date (months, days, year
enum in12_clock_date_setting_s {
    
    in12_set_date_month_state = 0,
    in12_set_date_day_state = 1,
    in12_set_date_year_state = 2,
    in12_clock_date_setting_finished_state = 3
    
}
volatile in12_clock_date_setting = 3;

// This enum keeps track of which weekday setting we're changing when the user wants
// to change the weekday
// (only lets you set the weekday or nothing, since there is only one parameter to change
enum in12_clock_weekday_setting_s {
    
    in12_set_weekday_day_state = 0,
    in12_clock_weekday_setting_finished_state = 1
    
}
volatile in12_clock_weekday_setting = 1;

// This enum keeps track of which time setting we're changing when the user wants
// to change the alarm time (hours, minutes, seconds
enum in12_clock_alarm_setting_s {
    
    in12_set_alarm_hours_state = 0,
    in12_set_alarm_minutes_state = 1,
    in12_set_alarm_seconds_state = 2,
    in12_clock_alarm_setting_finished_state = 3
    
}
volatile in12_clock_alarm_setting = 3;

// This enum keeps track of which brightness setting we're changing when the user wants
// to change the brightness
// (only lets you set the brightness or nothing, since there is only one parameter to change
enum in12_clock_brightness_setting_s {
    
    in12_set_brightness_value_state = 0,
    in12_clock_brightness_setting_finished_state = 1
    
}
volatile in12_clock_brightness_setting = 1;

enum in12_clock_24hr_setting_s {
    
    in12_set_24hr_value_state = 0,
    in12_clock_24hr_setting_finished_state = 1
    
}
volatile in12_clock_24hr_setting = 1;

enum in12_clock_alarm_enable_setting_s {
    
    in12_set_alarm_arm_state = 0,
    in12_clock_alarm_enable_finished_state = 1
    
}
volatile in12_clock_alarm_enable_setting = 1;

enum in12_backlight_color_setting_s {
    
    in12_backlight_black = 0,
    in12_backlight_red = 1,
    in12_backlight_green = 2,
    in12_backlight_blue = 3,
    in12_backlight_yellow = 4,
    in12_backlight_cyan = 5,
    in12_backlight_magenta = 6,
    in12_backlight_white = 7
    
}
volatile in12_backlight_color_setting = 0;

// This buffer keeps track of which characters are displayed on which tubes
// Copy a <= 8 character string into it
// characters [2] and [5] can only display *, _ and : (these are the colons)
char in12_display_buffer[9];

// this flag is used to keep track of if the display is enabled or not
// pressing the power button toggles this
volatile uint8_t in12_display_power_toggle_flag = 0;

// this function prints config status for misc I2C devices
void IN12I2CDevicesPrintStatus(void);

// sets up IN12 GPIO expander
void IN12GPIOExpanderInitialize(void);

// sets up backlight LED driver
void IN12BacklightInitialize(void);

// this function sets the brightness of the backlight
// backlight_brightness range is 0 to 255
void IN12BacklightSetBrightness(uint8_t backlight_brightness);

// this function sets the color of the backlight LEDs
// all arguments have range 0 to 255
void IN12BacklightSetUniformColor(uint8_t red_component, uint8_t green_component, uint8_t blue_component);

// this function initializes the logic board ETC counter
void IN12ETCInitialize(void);

// this function returns elapsed time in seconds (w/ 0.25 second granularity) for logic board from I2C elapsed time counter
double IN12GetETC(void);

// this function returns the number of power cycles for the logic board from I2C elapsed time counter
uint32_t IN12GetPowerCycles(void);

// this function reads the contents of the output registers of the IN12 GPIO expander, and sets or clears only the backlight LED enable signal
void IN12GPIOSetBacklightEnable(uint8_t led_enable_state);

// this function reads the contents of the output registers of the IN12 GPIO expander, and sets or clears only the ETC enable signal
void IN12GPIOSetETCEnable(uint8_t etc_enable_state);

// this function checks if the current time matches the alarm time and sets the buzzer
// if the alarm is armed.
void IN12AlarmCheckMatch(void);

// this function sets the state of the display board LEDs to match what clock_display_state enum is set to
void IN12SetMenuLEDs(void);

// this function initializes the devices on the IN12 carrier board and sets up internal peripherals within the PIC to drive the display
void IN12Initialize(void);

// this is the callback function for the multiplexing timer, specific to IN12 carrier
multiplexing_timer_callback_t IN12MultiplexingTimerHandler(void);

// this is the calback function for the brightness timer, specific to IN12 carrier
brightness_timer_callback_t IN12BrightnessTimerHandler(void);

// This function sets all IN12 tube anodes low
void blankIN12Anodes(void);

// This function blanks all IN12 cathodes
void blankIN12Cathodes(void);

// This function sets up the cathodes for driving tubes based on active_tube enum
void setIN12Anodes(void);

// This function sets the proper anodes to display the character passed 
// PASS A CHARACTER, NOT A NUMBER!
void setIN12Cathodes(char input_char);

// This function sets cathodes for the colons
// pass a colon number (0:1) and a character to display (:, ., and *)
void setIN12ColonCathodes(uint8_t colon_number, char input_char);

// this function powers on the IN12 carrier
void IN12PowerOn(void);

// this function powers off the IN12 carrier
void IN12PowerOff(void);

// This function sets the display board IO expander output
void IN12SetMenuLEDsGPIO(uint16_t output_data);

// This function updates the IN12 display based on the current state of what we want to display
// relies on global variables in in12_carrier and rtcc modules
void IN12updateClockDisplay(void);

// this function sets the brightness of the display based on what you pass it
// number must be between 10 and 100
void IN12SetDisplayBrightness(uint8_t input_brightness);

// this function sets the backlight color based on pushbutton input (based on in12_backlight_color_setting enum)
void IN12SetBacklightColorState(void);

// these functions are the handler functions for pressing used pushbuttons
pushbutton_input_0_callback_t power_pushbutton_callback(void);
pushbutton_input_1_callback_t left_pushbutton_callback(void);
pushbutton_input_2_callback_t right_pushbutton_callback(void);
pushbutton_input_3_callback_t up_pushbutton_callback(void);
pushbutton_input_4_callback_t down_pushbutton_callback(void);

#endif /* _IN12_CARRIER_H */

/* *****************************************************************************
 End of File
 */
