drewsum/Nixie_Clock/rev_b/sfw/U1001_Firmware/Nixie_Clock.X/ds1683_ETC.c

#include "ds1683_ETC.h"

#include <stdio.h>

#include "plib_i2c.h"

#include "error_handler.h"
#include "device_control.h"
#include "terminal_control.h"


// This function initializes a time of flight counter at passed address. Also pass pointer to error handler flag for device
void DS1683ETCInitialize(uint8_t device_address, volatile uint8_t *device_error_handler_flag) {

    // Write config data to config register on input temp sensor
    uint8_t output_data_array[2];
    output_data_array[0] = DS1683_CONFIG_REG;
    output_data_array[1] = DS1683_CONFIG_DATA;
    if(!I2CMaster_Write(device_address, output_data_array, 2)) {
        *device_error_handler_flag = 1;
    }
    while(i2cMasterObj.state != I2C_STATE_IDLE);

}

// This function gets the time of flight from counter at passed address. Also pass pointer to error handler flag for device
// returns on time in seconds with 0.25 second resolution
double DS1683GetETC(uint8_t device_address, volatile uint8_t *device_error_handler_flag) {
    
    uint8_t data_reg_pointer[1];
    uint8_t readBytes[4];
    data_reg_pointer[0] = DS1683_ETC_0_REG;
    if(!I2CMaster_WriteRead(device_address, &data_reg_pointer[0], 1, readBytes, 4)) {
        *device_error_handler_flag = 1;
    }
    while(i2cMasterObj.state != I2C_STATE_IDLE);
    
    // convert received data to volts
    uint32_t received_data = ((readBytes[3] << 24) | (readBytes[2] << 16) | (readBytes[1] << 8) | (readBytes[0]));
    double return_val = ((double) received_data) * 0.25;
    return return_val;

}

// This function gets the event count from counter at passed address. Also pass pointer to error handler flag for device
uint32_t DS1683GetEventCount(uint8_t device_address, volatile uint8_t *device_error_handler_flag) {
 
    uint8_t data_reg_pointer[1];
    uint8_t readBytes[2];
    data_reg_pointer[0] = DS1683_EVENT_0_REG;
    if(!I2CMaster_WriteRead(device_address, data_reg_pointer, 1, readBytes, 2)) {
        *device_error_handler_flag = 1;
    }
    while(i2cMasterObj.state != I2C_STATE_IDLE);
    
    if (i2cMasterObj.state == I2C_STATE_IDLE) {
        // convert received data to volts
        return ((readBytes[1] << 8) | (readBytes[0]));
    }
    else {
        *device_error_handler_flag = 1;
        return 0;
    }
    
    
}

// this function prints status and config data for a ocunter at passed address
void DS1683PrintStatus(uint8_t device_address, volatile uint8_t *device_error_handler_flag) {
 
    // read status register first
    uint8_t data_reg_pointer[1];
    uint8_t readBytes[16];
    data_reg_pointer[0] = DS1683_STATUS_REG;
    if(!I2CMaster_WriteRead(device_address, data_reg_pointer, 1, readBytes, 1)) {
        *device_error_handler_flag = 1;
    }
    while(i2cMasterObj.state != I2C_STATE_IDLE);
    
    uint8_t read_event_af = (readBytes[0] >> 1) & 0b1;
    uint8_t read_etc_af = (readBytes[0]) & 0b1;
    
    // read event count alarm register
    data_reg_pointer[0] = DS1683_EVENT_ALRM_0_REG;
    if(!I2CMaster_WriteRead(device_address, data_reg_pointer, 1, readBytes, 1)) {
        *device_error_handler_flag = 1;
    }
    while(i2cMasterObj.state != I2C_STATE_IDLE);
    uint16_t read_event_alarm = (readBytes[1] << 8) | readBytes[0];
    
    // read ETC alarm limit
    data_reg_pointer[0] = DS1683_ETC_0_REG;
    if(!I2CMaster_WriteRead(device_address, data_reg_pointer, 1, readBytes, 4)) {
        *device_error_handler_flag = 1;
    }
    while(i2cMasterObj.state != I2C_STATE_IDLE);
    uint32_t read_etc_alarm = ((readBytes[3] << 24) | (readBytes[2] << 16) | (readBytes[1] << 8) | (readBytes[0]));
    
    // read config register
    data_reg_pointer[0] = DS1683_CONFIG_REG;
    if(!I2CMaster_WriteRead(device_address, data_reg_pointer, 1, readBytes, 1)) {
        *device_error_handler_flag = 1;
    }
    while(i2cMasterObj.state != I2C_STATE_IDLE);
    uint8_t read_etc_alarm_en = (readBytes[0] >> 2) & 0b1;
    uint8_t read_event_alarm_en = (readBytes[0] >> 1) & 0b1;
    uint8_t read_alarm_pol = readBytes[0] & 0b1;
    
    // read user NVM
    data_reg_pointer[0] = DS1683_USR_MEM_0_REG;
    if(!I2CMaster_WriteRead(device_address, data_reg_pointer, 1, readBytes, 16)) {
        *device_error_handler_flag = 1;
    }
    while(i2cMasterObj.state != I2C_STATE_IDLE);
    uint8_t readUserNVM[16];
    uint8_t i;
    for(i=0; i<16; i++)
    {
        readUserNVM[i] = readBytes[i];
    }
    
    // print out received data
    terminalTextAttributes(GREEN_COLOR, BLACK_COLOR, BOLD_FONT);
    printf("DS1683 Elapsed Time/Event counter, located at 0x%02X\r\n", device_address);
    if (read_etc_alarm_en) terminalTextAttributes(GREEN_COLOR, BLACK_COLOR, NORMAL_FONT);
    else terminalTextAttributes(RED_COLOR, BLACK_COLOR, NORMAL_FONT);
    printf("    ETC Alarm is %s\r\n", read_etc_alarm_en ? "enabled" : "disabled");
    if (read_event_alarm_en) terminalTextAttributes(GREEN_COLOR, BLACK_COLOR, NORMAL_FONT);
    else terminalTextAttributes(RED_COLOR, BLACK_COLOR, NORMAL_FONT);
    printf("    Event Alarm is %s\r\n", read_event_alarm_en ? "enabled" : "disabled");
    terminalTextAttributes(GREEN_COLOR, BLACK_COLOR, NORMAL_FONT);
    printf("    Alarm pin polarity is %s\r\n", read_alarm_pol ? "active high" : "active low");
    if (read_event_af) terminalTextAttributes(GREEN_COLOR, BLACK_COLOR, NORMAL_FONT);
    else terminalTextAttributes(RED_COLOR, BLACK_COLOR, NORMAL_FONT);
    printf("    Event Alarm has %s\r\n", read_event_af ? "triggered" : "not triggered");
    if (read_etc_af) terminalTextAttributes(GREEN_COLOR, BLACK_COLOR, NORMAL_FONT);
    else terminalTextAttributes(GREEN_COLOR, BLACK_COLOR, NORMAL_FONT);
    terminalTextAttributes(RED_COLOR, BLACK_COLOR, NORMAL_FONT);
    printf("    ETC Alarm has %s\r\n", read_etc_af ? "triggered" : "not triggered");
    terminalTextAttributes(GREEN_COLOR, BLACK_COLOR, NORMAL_FONT);
    printf("    Event Alarm threshold set to %u events\r\n", read_event_alarm);
    printf("    ETC Alarm set to %.3f seconds\r\n", read_etc_alarm * 0.25);
    for(i=0; i<16; i++) {
        printf("    User NVM Data %u: 0x%02X\r\n", i, readUserNVM[i]);
    }       
    terminalTextAttributesReset();
}
