drewsum/Nixie_Clock/rev_b/sfw/U1001_Firmware/Nixie_Clock.X/main.h

/* ************************************************************************** */
/** Descriptive File Name

  @Company
    Drew Maatman

  @File Name
    main.h

  @Summary
    Includes high level project metadata

  @Description
    Includes high level project metadata
 */
/* ************************************************************************** */

#ifndef _MAIN_H    /* Guard against multiple inclusion */
#define _MAIN_H

#define FIRMWARE_VERSION_STR        "0.95"
#define PLATFORM_REVISION_STR       "B"
#define PROJECT_DATE_STR            "February 2024"
#define PROJECT_NAME_STR            "Nixie Clock"
#define PROJECT_REPOSITORY_STR      "https://github.com/drewsum/Nixie_Clock"

#endif /* _EXAMPLE_FILE_NAME_H */

/* *****************************************************************************
 End of File
 */
